sparkfun/OpenLog_Artemis/Firmware/OpenLog_Artemis/zmodem.h

// From: http://www.raspberryginger.com/jbailey/minix/html/zmodem_8h-source.html
#ifndef ZMODEM_H
#define ZMODEM_H
#include "zmodem_config.h"
#include "zmodem_fixes.h"
/*
 *   Z M O D E M . H     Manifest constants for ZMODEM
 *    application to application file transfer protocol
 *    05-23-87  Chuck Forsberg Omen Technology Inc
 */
#define ZPAD '*'        /* 052 Padding character begins frames */
#define ZDLE 030        /* Ctrl-X Zmodem escape - `ala BISYNC DLE */
#define ZDLEE (ZDLE^0100)       /* Escaped ZDLE as transmitted */
#define ZBIN 'A'        /* Binary frame indicator */
#define ZHEX 'B'        /* HEX frame indicator */
#define ZBIN32 'C'      /* Binary frame with 32 bit FCS */

/* Frame types (see array "frametypes" in zm.c) */
#define ZRQINIT 0       /* Request receive init */
#define ZRINIT  1       /* Receive init */
#define ZSINIT 2        /* Send init sequence (optional) */
#define ZACK 3          /* ACK to above */
#define ZFILE 4         /* File name from sender */
#define ZSKIP 5         /* To sender: skip this file */
#define ZNAK 6          /* Last packet was garbled */
#define ZABORT 7        /* Abort batch transfers */
#define ZFIN 8          /* Finish session */
#define ZRPOS 9         /* Resume data trans at this position */
#define ZDATA 10        /* Data packet(s) follow */
#define ZEOF 11         /* End of file */
#define ZFERR 12        /* Fatal Read or Write error Detected */
#define ZCRC 13         /* Request for file CRC and response */
#define ZCHALLENGE 14   /* Receiver's Challenge */
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
